jacobjuneau6/FPL/FPL/symbols/ul_S80KS5123GABHV020-3/PG-BGA-24-801.step

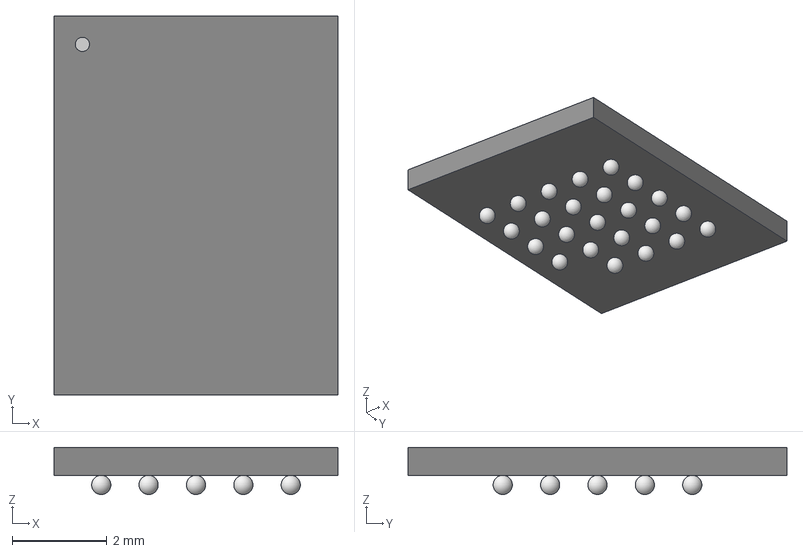
[picture p17: CAD file, 2026-04-07]
FPL/symbols/ul_S80KS5123GABHV020-3/PG-BGA-24-801.step
5.99 x 8.00 x 0.993 mm
