jacobjuneau6/FPL/FPL/symbols/W9825G6KH-6/W9825G6KH-6.step

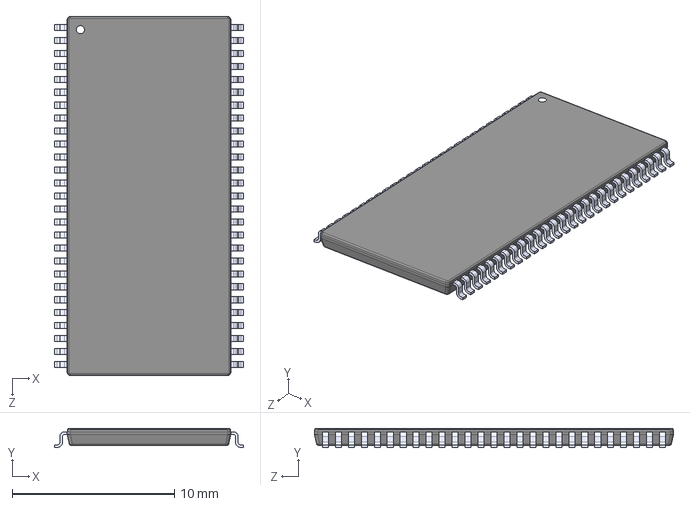
[picture p18: CAD file, 2026-04-07]
FPL/symbols/W9825G6KH-6/W9825G6KH-6.step
11.7 x 1.20 x 22.2 mm
