jacobjuneau6/FPL/FPL/symbols/WL-SMSW_1204_A/WL-SMSW_1204_A.step

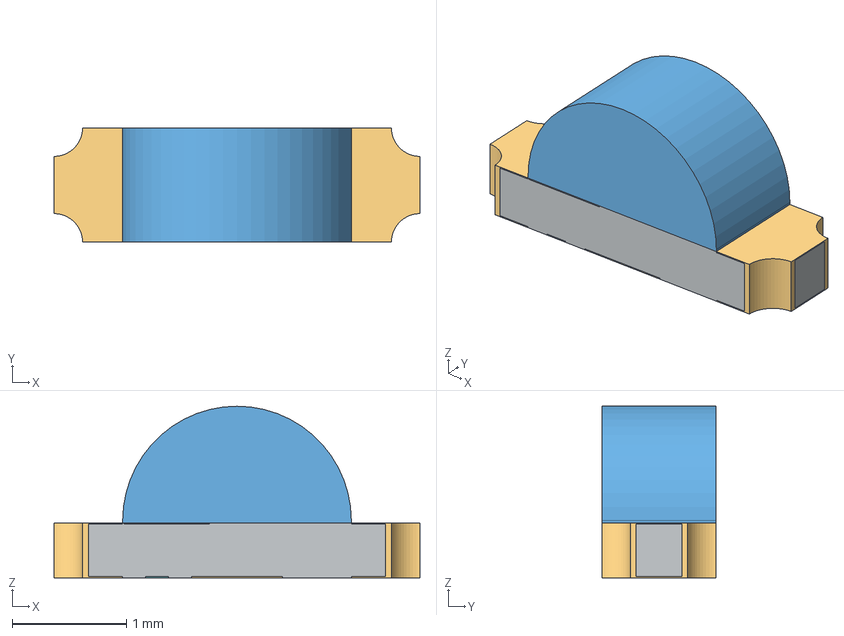
[picture p19: CAD file, 2026-04-07]
FPL/symbols/WL-SMSW_1204_A/WL-SMSW_1204_A.step
3.20 x 1.00 x 1.50 mm
Contact x 7
Doom
