jacobjuneau6/FPL/FPL/symbols/LD1117S33CTR--3DModel-STEP-418109.STEP

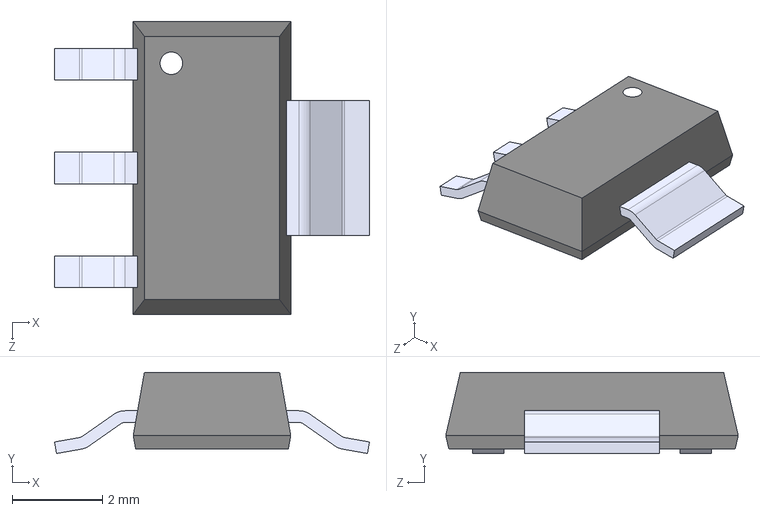
[picture p20: CAD file, 2026-04-07]
FPL/symbols/LD1117S33CTR--3DModel-STEP-418109.STEP
7.00 x 1.80 x 6.50 mm
