jacobjuneau6/FPL/FPL/symbols/W25Q128JVSIQ TR.STEP

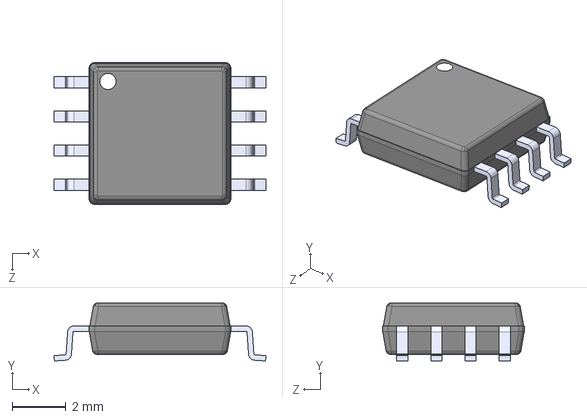
[picture p21: CAD file, 2026-04-07]
FPL/symbols/W25Q128JVSIQ TR.STEP
7.90 x 2.16 x 5.28 mm
